AndyChiu/KSTG/stl_Sample/KSTG_Sample2.scad

// 鍵帽儲存托盤產生器
// Keycap Storage Tray Generator
include <KSTG_Base.SCAD>

// 可複製此樣板檔依照自己需求另存新檔
// 以便以檔案區隔樣式

// 存放盒子的大小:
BoxSize_L1 = 193; //長度(水平)
BoxSize_W1 = 122; //寬度(垂直)
BoxSize_H1 = 55;  //高度

// 外圍厚度
Tray_Fence_T = 1;  //厚度
Tray_Fence_H = 6;  //高度

// 分隔片
Tray_Separator_T = 1;  //厚度
Tray_Separator_H = 5;  //高度 要高於上一層與鍵帽間的間隙
Tray_Separator_L = 3;  //短隔板長度

// 分隔片(長寬區分/尚未使用)
//Tray_Separator_T_L = 1;  //長(水平) 厚度
//Tray_Separator_T_W = 2;  //寬(垂直) 厚度
//Tray_Separator_H_L = 5;  //長(水平) 高度
//Tray_Separator_H_W = 5;  //寬(垂直) 高度

// 底板
Tray_Bottom_L = 5; //底部分隔板至到底板寬度
Tray_Bottom_T = 2; //底板厚度

//常見鍵帽高度表:
//SA  16.5mm  Cherry 9.4mm
//OEM 11.9mm  TAI HAO 14.8
//XDA 9.1mm   DSA 7.6
//ADA 8mm (18.2x18.2mm )
//適用於 Tray_Column_H 參數

//四角落立柱高度
//堆疊托盤時可墊高避免直接碰觸鍵帽
Tray_Column_H = 14; // 高度 可依照鍵帽高度調整
Tray_Column_T = 2;  // 厚度
Tray_Column_L = 15; // 長面長度
Tray_Column_W = 15; // 寬面長度 

//放置鍵帽空間
Keycaps_Space_L = 18.5;
Keycaps_Space_W = 18.5;

//垂直分隔片樣式
// 0 不需要
// 1 全部
// 2 短隔板無底板
// 3 短隔板有底板

Tray_VS_Type = 0;

//多餘空間處理方式
//How to use the extra space
// 0 不處理，照原本盒子大小產生外圍
// 1 不處理，僅列印鍵帽所需空間
// 2 角落填補剩餘空間
ExtraSpaceUse = 2;

//是否顯示文字標記 0關/1開
ShowText = 1 ;

//清除分隔片與底板
//請參考F5後帶出的座標數值
//例如：
// Tray_Separator_Cut_L=[
// [1,1],[2,1],[3,1],[1,2]
// ];

// 長(水平)分隔片 紅色
Tray_Separator_Cut_L=[
];
// 寬(垂直)分隔片 藍色 -vnm,     
Tray_Separator_Cut_W=[
];
// 交錯點 綠色 長寬分隔片交會處
// 須手動清除交錯點
Tray_Separator_Cut_C=[
];
// 長(水平)底板 紅色
Tray_Separator_Cut_LB=[
];
// 寬(垂直)底板 藍色
Tray_Separator_Cut_WB=[
];
